TecnoEduHub/CONAE-Cansat-2026/desafio/ETAPA 4 - Construcción y validación del CANSAT/ Misión Primaria/Firmware/tests_mpu/MPU-6050-GY-521-Accelerometer-Schematic.jpg

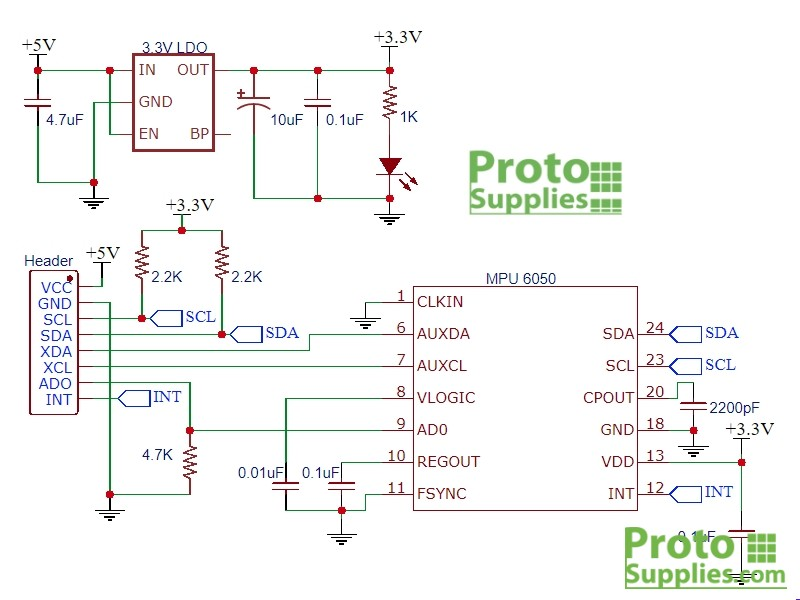
desafio/ETAPA 4 - Construcción y validación del CANSAT/ Misión Primaria/Firmware/tests_mpu/MPU-6050-GY-521-Accelerometer-Schematic.jpg
