TecnoEduHub/CONAE-Cansat-2026/desafio/ETAPA 4 - Construcción y validación del CANSAT/cam/ESP32-CAM-AI-Thinker Schematic Diagram.png

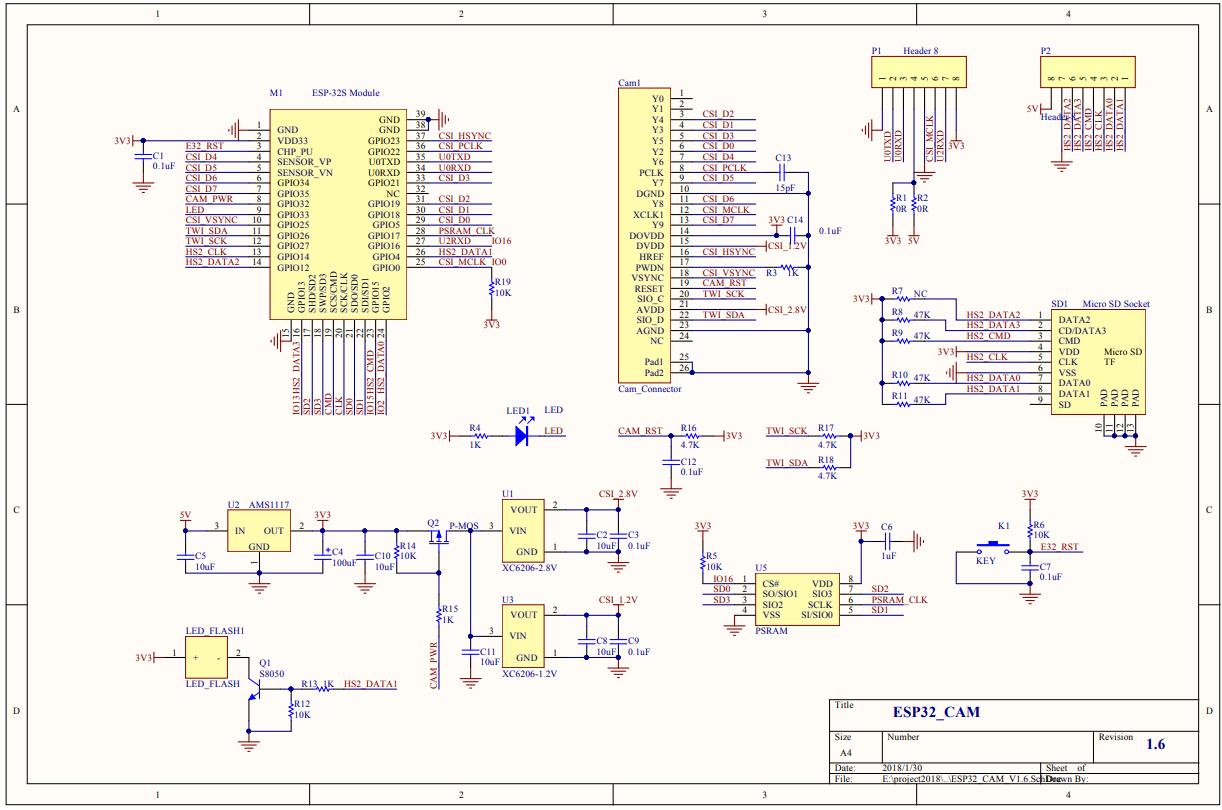
desafio/ETAPA 4 - Construcción y validación del CANSAT/cam/ESP32-CAM-AI-Thinker Schematic Diagram.png
