TecnoEduHub/CONAE-Cansat-2026/docs/cronograma.png

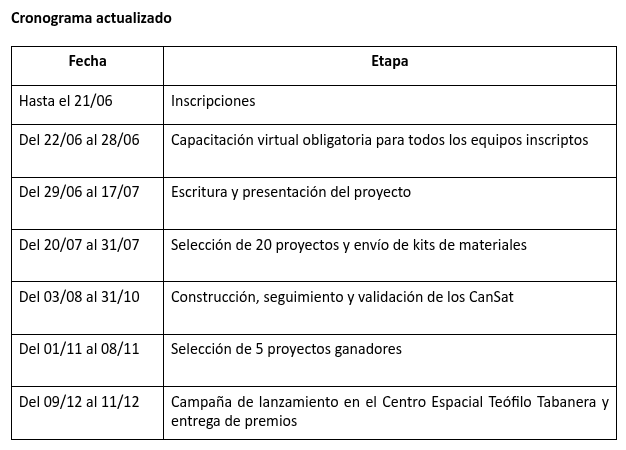
docs/cronograma.png
