TecnoEduHub/CONAE-Cansat-2026/desafio/ETAPA 4 - Construcción y validación del CANSAT/cam/esp32-cam_01.jpg

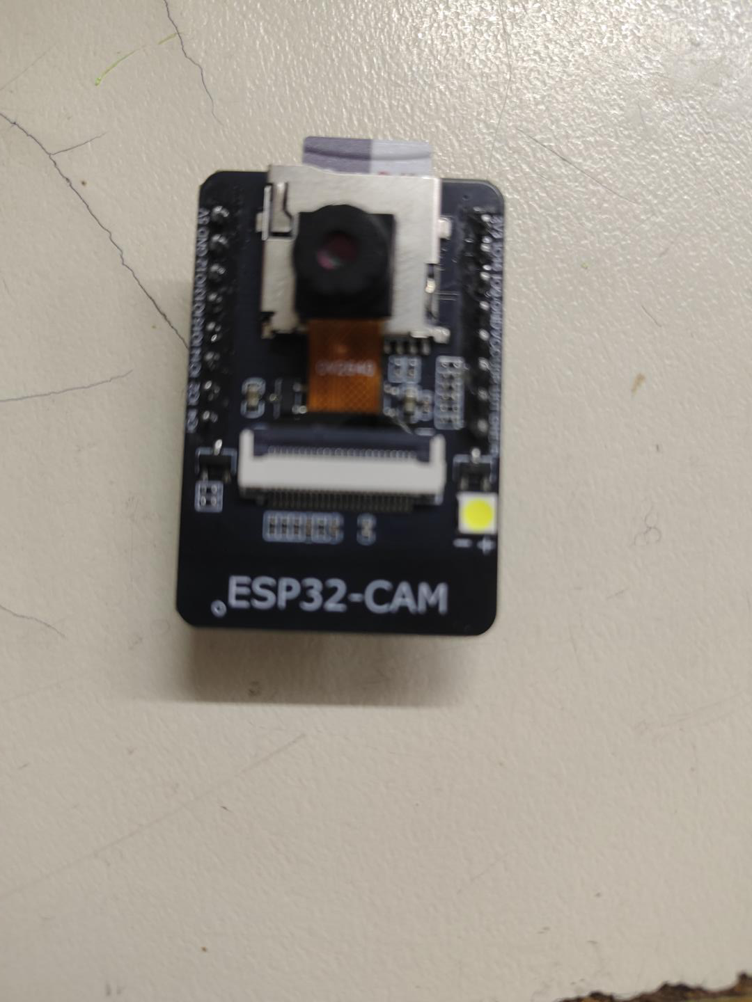
desafio/ETAPA 4 - Construcción y validación del CANSAT/cam/esp32-cam_01.jpg
