TecnoEduHub/CONAE-Cansat-2026/desafio/ETAPA 4 - Construcción y validación del CANSAT/cam/esquemático.jpg

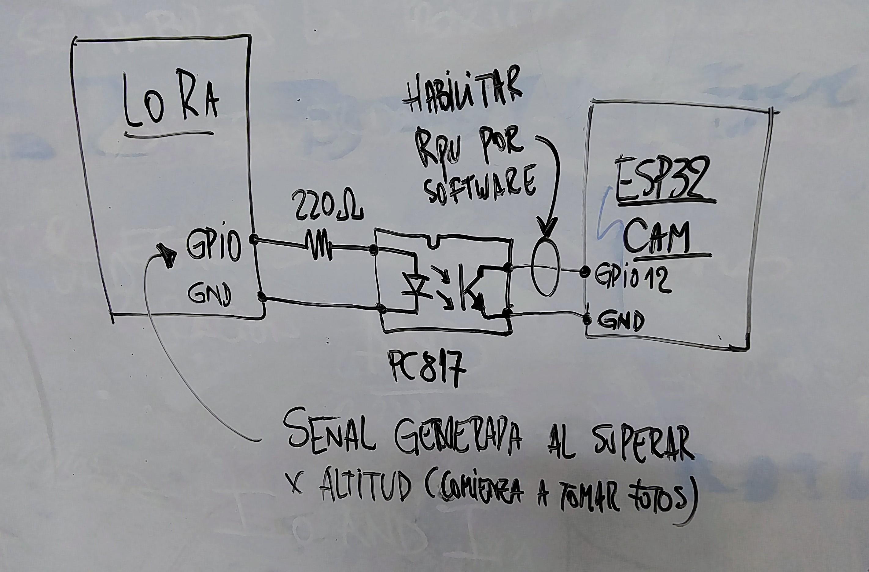
desafio/ETAPA 4 - Construcción y validación del CANSAT/cam/esquemático.jpg
