TecnoEduHub/CONAE-Cansat-2026/desafio/ETAPA 4 - Construcción y validación del CANSAT/cam/photos/foto_00002.jpg

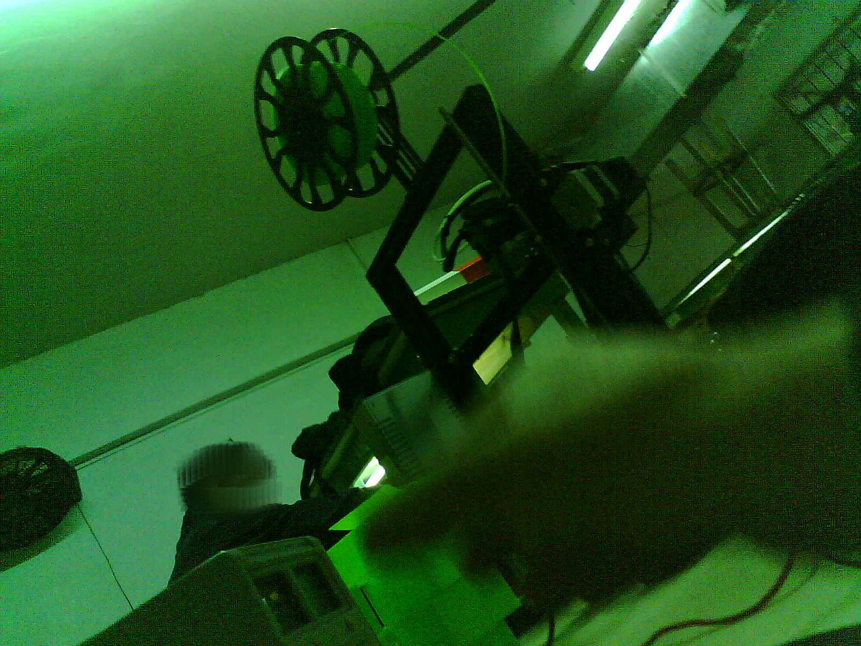
desafio/ETAPA 4 - Construcción y validación del CANSAT/cam/photos/foto_00002.jpg
