TecnoEduHub/CONAE-Cansat-2026/desafio/ETAPA 4 - Construcción y validación del CANSAT/cam/photos/foto_00003.jpg

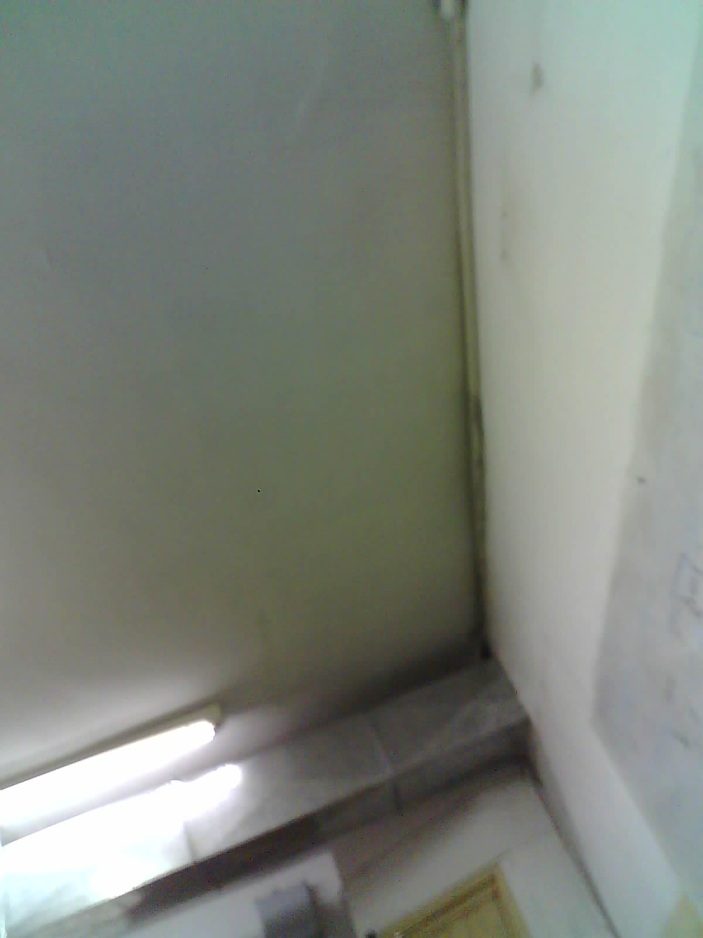
desafio/ETAPA 4 - Construcción y validación del CANSAT/cam/photos/foto_00003.jpg
