TecnoEduHub/CONAE-Cansat-2026/desafio/ETAPA 4 - Construcción y validación del CANSAT/cam/photos/foto_00010.jpg

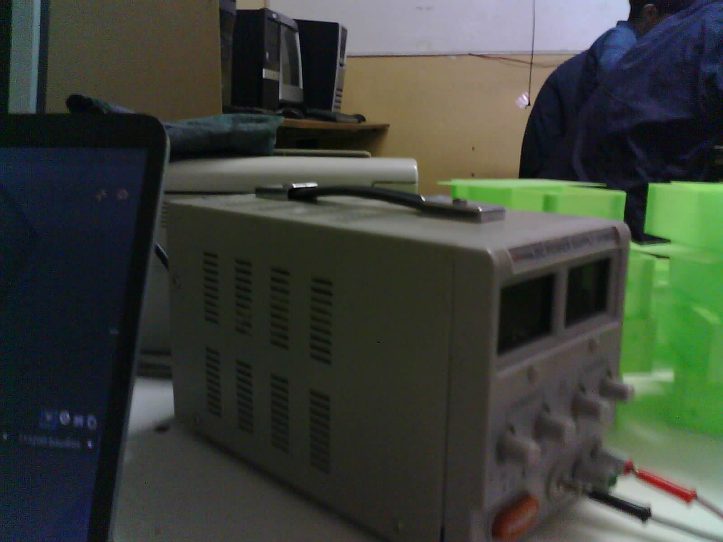
desafio/ETAPA 4 - Construcción y validación del CANSAT/cam/photos/foto_00010.jpg
