TecnoEduHub/CONAE-Cansat-2026/desafio/ETAPA 4 - Construcción y validación del CANSAT/cansat_3d/registro/IMG-20261006-WA0001.jpg

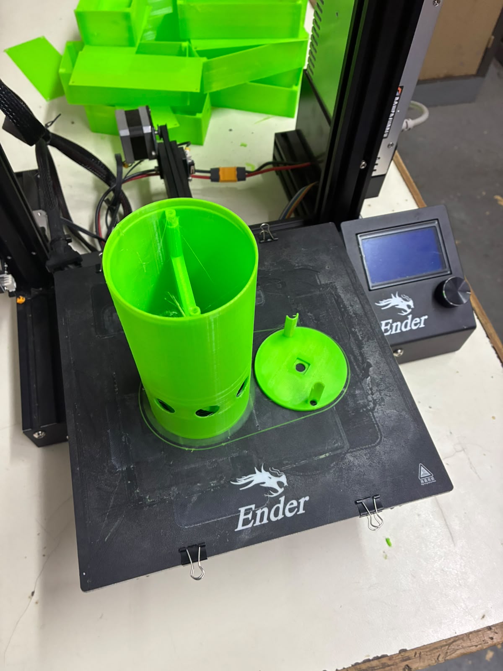
desafio/ETAPA 4 - Construcción y validación del CANSAT/cansat_3d/registro/IMG-20261006-WA0001.jpg
