TecnoEduHub/CONAE-Cansat-2026/desafio/ETAPA 4 - Construcción y validación del CANSAT/Estación Terrena/Case/images/IMG_20250914_142135.jpg

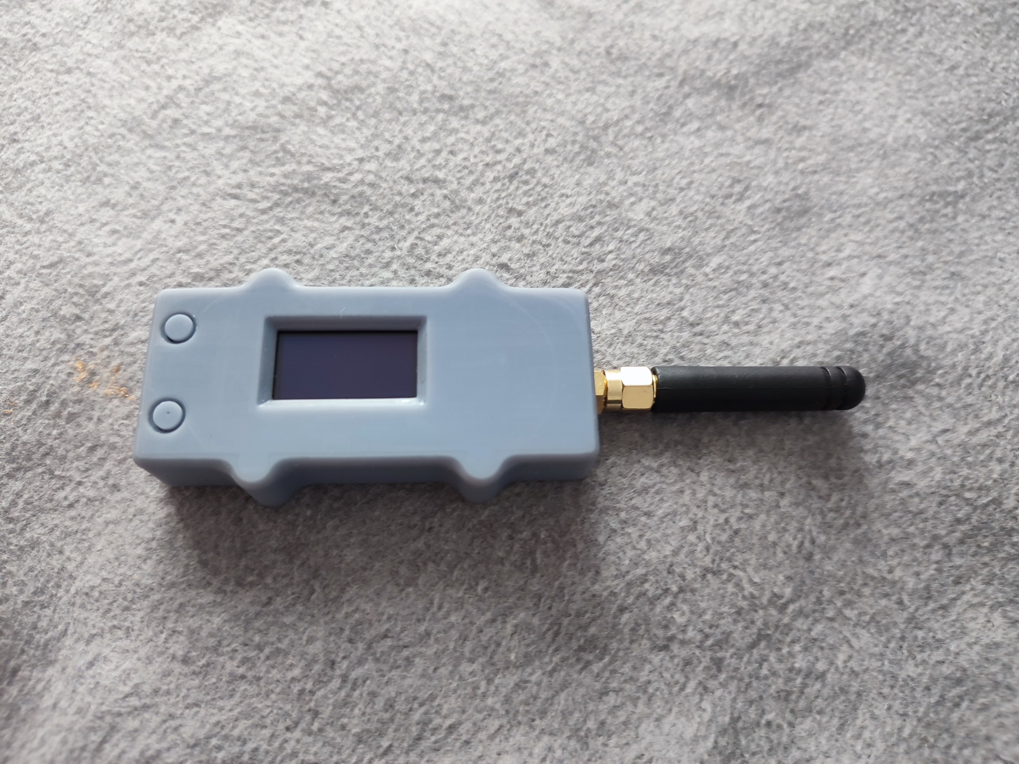
desafio/ETAPA 4 - Construcción y validación del CANSAT/Estación Terrena/Case/images/IMG_20250914_142135.jpg
