TecnoEduHub/CONAE-Cansat-2026/desafio/ETAPA 4 - Construcción y validación del CANSAT/Estación Terrena/Case/images/Meshtastic_heltec_v3_gehäuse_1.1.png

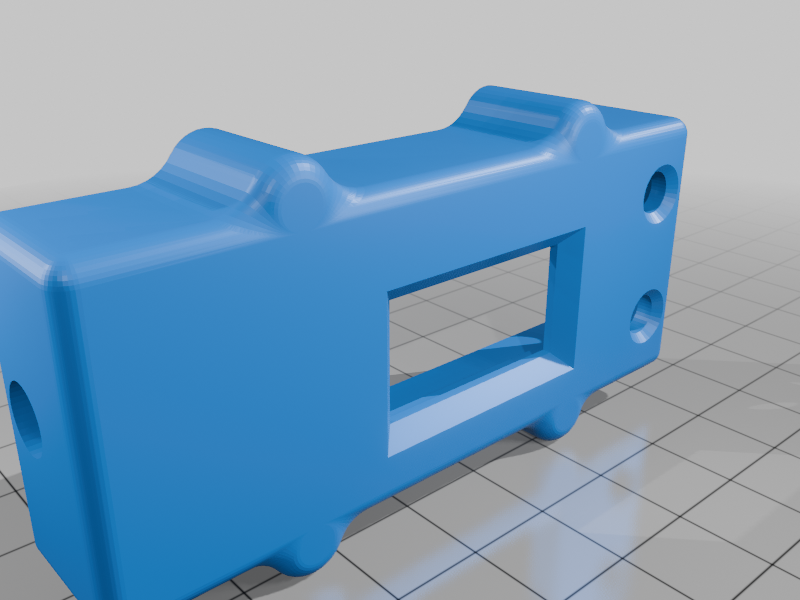
desafio/ETAPA 4 - Construcción y validación del CANSAT/Estación Terrena/Case/images/Meshtastic_heltec_v3_gehäuse_1.1.png
