TecnoEduHub/CONAE-Cansat-2026/desafio/ETAPA 4 - Construcción y validación del CANSAT/Estación Terrena/Dashboard/Pantallas/SerialStudio_02_Dashboard.png

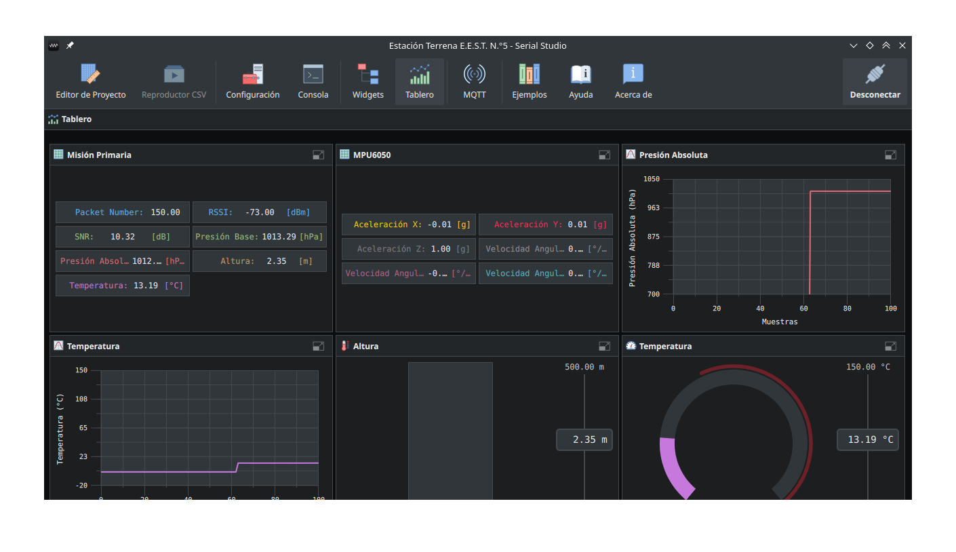
desafio/ETAPA 4 - Construcción y validación del CANSAT/Estación Terrena/Dashboard/Pantallas/SerialStudio_02_Dashboard.png
