TecnoEduHub/CONAE-Cansat-2026/desafio/ETAPA 4 - Construcción y validación del CANSAT/ Misión Primaria/Firmware/sketch_lora_rx/logo_eest5.h

#pragma once
#include <Arduino.h>

const uint8_t logo_eest5_48x48[] PROGMEM = {
  0x00, 0x00, 0x00, 0x00, 0x00, 0x00, 0x80, 0x87, 0xFF, 0xFF, 0x01, 0x00,
  0xE0, 0x87, 0xFF, 0xFF, 0x01, 0x00, 0xF0, 0x87, 0xFF, 0xFF, 0x01, 0x00,
  0xF8, 0x87, 0xFF, 0xFF, 0x01, 0x00, 0xFC, 0x87, 0xFF, 0xFF, 0x01, 0x00,
  0xFE, 0x87, 0xFF, 0xFF, 0x01, 0x00, 0xFE, 0x87, 0xFF, 0xFF, 0x01, 0x00,
  0xFF, 0x87, 0xFF, 0xFF, 0x01, 0x00, 0xFF, 0x07, 0x00, 0x00, 0x00, 0x00,
  0xFF, 0x07, 0x00, 0x00, 0x00, 0x00, 0xFF, 0x07, 0x00, 0x00, 0x00, 0x00,
  0xFF, 0x07, 0x00, 0x00, 0x00, 0x00, 0xFF, 0x87, 0xFF, 0xFF, 0xFF, 0xFF,
  0xFE, 0x87, 0xFF, 0xFF, 0xFF, 0xFF, 0xFE, 0x87, 0xFF, 0xFF, 0xFF, 0xFF,
  0xFC, 0x87, 0xFF, 0xFF, 0xFF, 0xFF, 0xFC, 0x87, 0xFF, 0xFF, 0xFF, 0xFF,
  0xFC, 0x87, 0xFF, 0xFF, 0xFF, 0xFF, 0xFE, 0x87, 0xFF, 0xFF, 0xFF, 0xFF,
  0xFE, 0x87, 0xFF, 0xFF, 0xFF, 0xFF, 0xFF, 0x87, 0xFF, 0xFF, 0xFF, 0xFF,
  0xFF, 0x07, 0x00, 0x00, 0x00, 0x00, 0xFF, 0x07, 0x00, 0x00, 0x00, 0x00,
  0xFF, 0x07, 0x00, 0x00, 0x00, 0x00, 0xFF, 0x07, 0x00, 0x00, 0x00, 0x00,
  0xFF, 0x87, 0xFF, 0xFF, 0xE1, 0x01, 0xFE, 0x87, 0xFF, 0xFF, 0xE1, 0x07,
  0xFE, 0x87, 0xFF, 0xFF, 0xE1, 0x0F, 0xFC, 0x87, 0xFF, 0xFF, 0xE1, 0x1F,
  0xFC, 0x87, 0xFF, 0xFF, 0xE1, 0x3F, 0xF8, 0x87, 0xFF, 0xFF, 0xE1, 0x3F,
  0xF0, 0x87, 0xFF, 0xFF, 0xE1, 0x7F, 0xC0, 0x87, 0xFF, 0xFF, 0xE1, 0x7F,
  0x00, 0x80, 0xFF, 0xFF, 0xE1, 0x7F, 0x00, 0x00, 0x00, 0x00, 0xE0, 0xFF,
  0x00, 0x00, 0x00, 0x00, 0xE0, 0xFF, 0x00, 0x00, 0x00, 0x00, 0xE0, 0xFF,
  0x00, 0x80, 0xFF, 0xFF, 0xE1, 0x7F, 0x00, 0x80, 0xFF, 0xFF, 0xE1, 0x7F,
  0x00, 0x80, 0xFF, 0xFF, 0xE1, 0x7F, 0x00, 0x80, 0xFF, 0xFF, 0xE1, 0x3F,
  0x00, 0x80, 0xFF, 0xFF, 0xE1, 0x3F, 0x00, 0x80, 0xFF, 0xFF, 0xE1, 0x1F,
  0x00, 0x80, 0xFF, 0xFF, 0xE1, 0x0F, 0x00, 0x80, 0xFF, 0xFF, 0xE1, 0x07,
  0x00, 0x80, 0xFF, 0xFF, 0xE1, 0x01, 0x00, 0x00, 0x00, 0x00, 0x00, 0x00
};
